ahesselman/BoatLight/Documents/Images/Lamp with stand.png

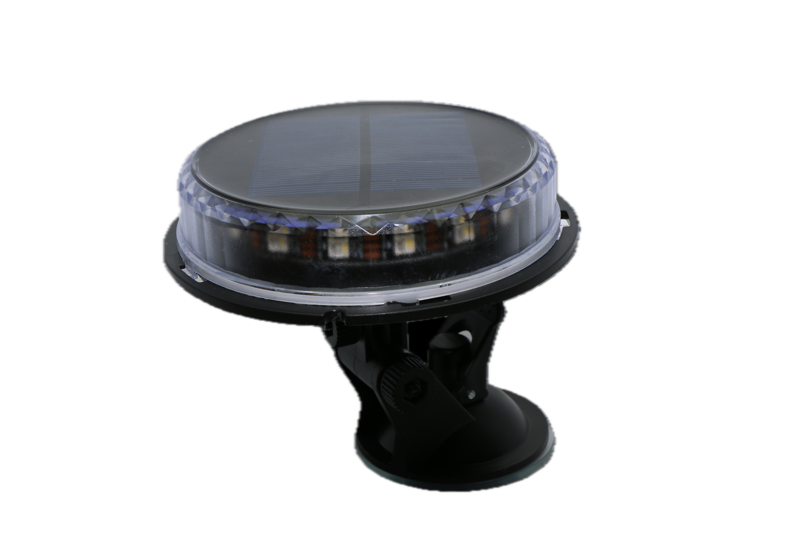
Documents/Images/Lamp with stand.png
