ahesselman/BoatLight/Documents/Images/Light modes.png

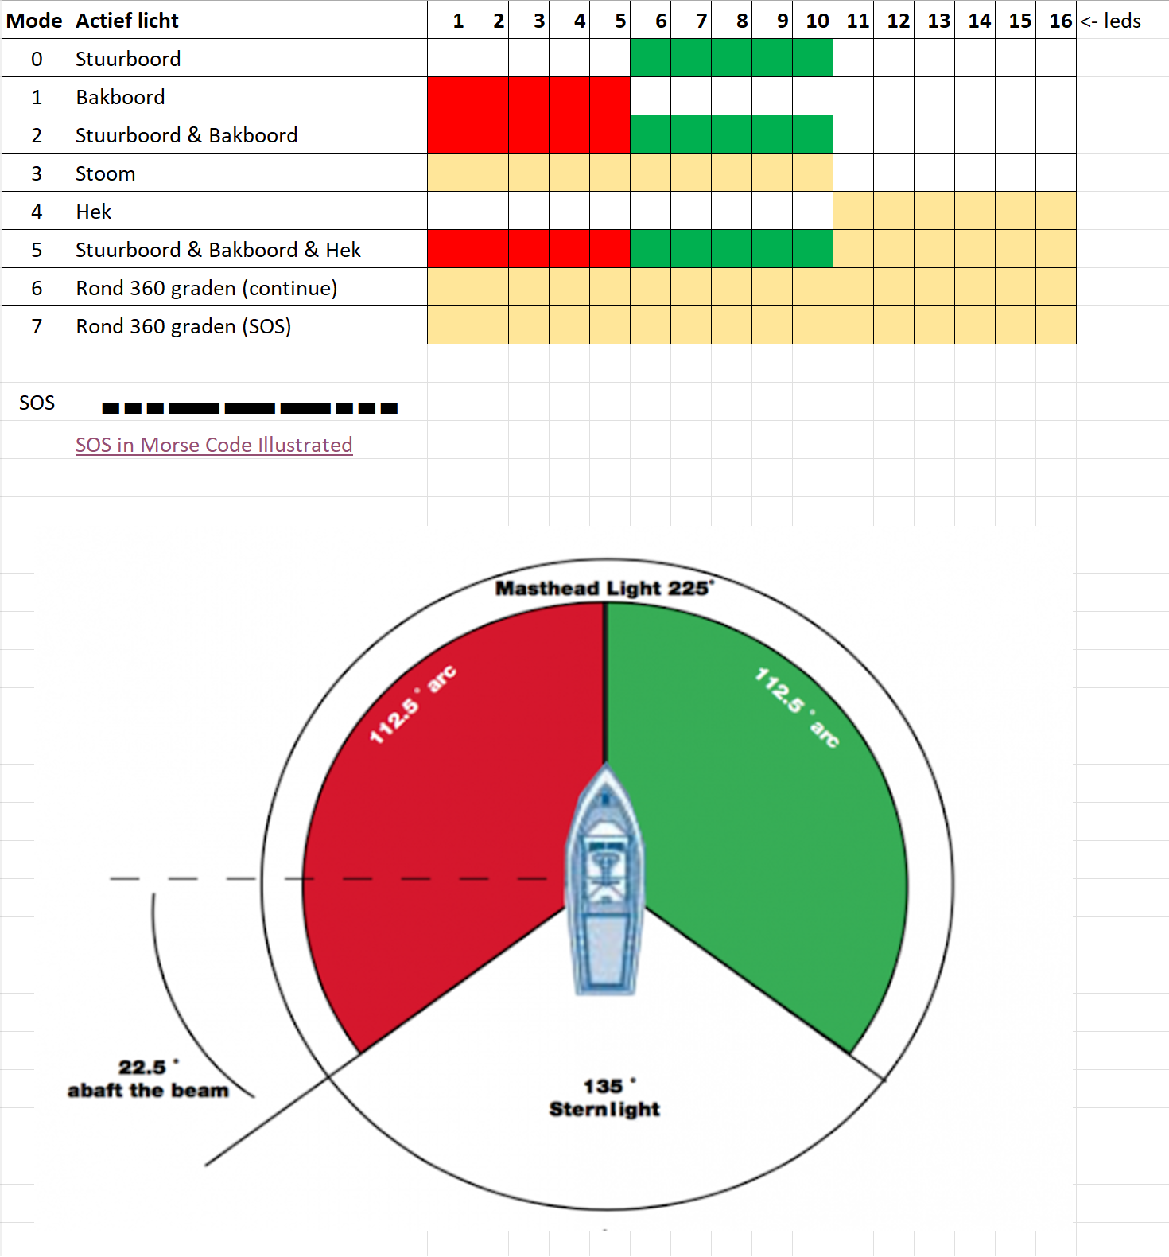
Documents/Images/Light modes.png
