ahesselman/BoatLight/Documents/Images/Remote.png

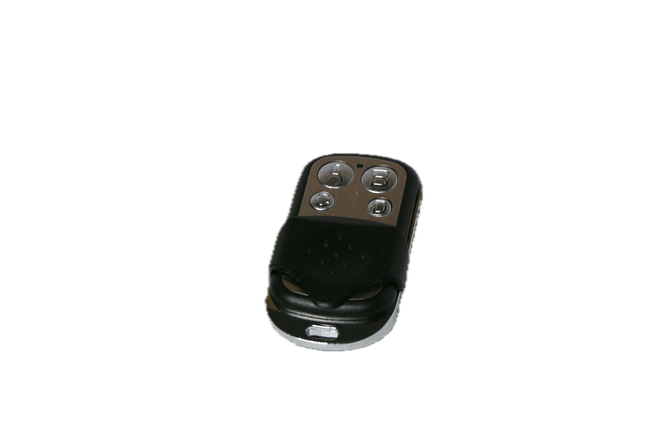
Documents/Images/Remote.png
