ahesselman/BoatLight/Tests/LedStrip/LedStrip.ino

#include <Adafruit_NeoPixel.h>
#ifdef __AVR__
 #include <avr/power.h>
#endif

#define PIN        0

#define NUMPIXELS 16

Adafruit_NeoPixel pixels(NUMPIXELS, PIN, NEO_GRBW + NEO_KHZ800);

#define DELAYVAL 500

void setup() {

#if defined(__AVR_ATtiny85__) && (F_CPU == 16000000)
  clock_prescale_set(clock_div_1);
#endif


  pixels.begin();
}

void loop() {
  pixels.clear();

  for(int i=0; i<NUMPIXELS; i++) { 

    // pixels.Color() takes RGB values, from 0,0,0 up to 255,255,255
    // Here we're using a moderately bright green color:
    pixels.setPixelColor(i, pixels.Color(0, 0, 0, 255));

    pixels.show();

    delay(DELAYVAL);
  }
}
